BogdanTheGeek/ch32fun-audio/samples.h

// RIFF: RIFF
// Overall size: 56452 bytes
// WAVE: WAVE
// Format chunk marker: fmt 
// Length of format: 16 bytes
// Format type: 1
// Channels: 1
// Sample rate: 32000 Hz
// Byte rate: 64000 bytes/sec
// Block align: 2 bytes
// Bits per sample: 16 bits
// Data chunk header: data
// Data size: 56416 bytes
#include <stdint.h>
#include <assert.h>


static const uint8_t samples[] = {
128, 224, 248, 254, 5, 129, 224, 7, 254, 1, 128, 224, 248, 254, 7, 130, 224, 248, 254, 6, 
129, 224, 248, 254, 5, 129, 224, 248, 254, 5, 128, 224, 248, 254, 5, 129, 224, 248, 254, 2, 
128, 95, 215, 237, 250, 126, 95, 183, 241, 254, 128, 224, 23, 253, 252, 126, 31, 167, 245, 250, 
126, 95, 151, 254, 0, 128, 31, 135, 205, 248, 126, 159, 248, 1, 255, 127, 224, 248, 1, 252, 
126, 224, 248, 9, 252, 127, 95, 248, 254, 4, 130, 224, 248, 254, 3, 129, 224, 248, 254, 9, 
131, 225, 248, 254, 20, 132, 225, 248, 254, 26, 134, 225, 248, 254, 26, 133, 225, 248, 254, 15, 
132, 224, 248, 254, 14, 131, 224, 248, 9, 255, 127, 223, 231, 245, 251, 125, 223, 135, 221, 242, 
122, 222, 119, 161, 233, 122, 158, 167, 149, 229, 122, 30, 103, 141, 225, 121, 158, 215, 189, 239, 
123, 158, 231, 213, 252, 127, 159, 215, 254, 2, 129, 224, 248, 254, 14, 131, 224, 248, 254, 13, 
130, 224, 248, 254, 10, 129, 224, 248, 254, 7, 128, 159, 248, 254, 2, 128, 224, 7, 245, 250, 
125, 159, 71, 213, 244, 124, 95, 7, 201, 244, 124, 94, 215, 173, 235, 124, 159, 199, 249, 247, 
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
105, 156, 71, 254, 45, 147, 228, 248, 125, 235, 115, 28, 135, 85, 250, 136, 227, 248, 254, 4, 
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
};
static_assert(sizeof(samples) % 5 == 0, "Something went wrong, buffer size must be a multiple of 5 bytes");
